philipparndt/opentherm-wolf-cwl/openspec/changes/archive/2026-04-25-esp32-documentation/tasks.md

## 1. Documentation

- [x] 1.1 Create `esp32/README.md` — hardware components, wiring, build/flash instructions, configuration, MQTT reference, OLED/encoder usage
