philipparndt/opentherm-wolf-cwl/openspec/changes/archive/2026-04-26-schedule-list-grouping/tasks.md

## 1. Implementation

- [x] 1.1 Update `daysStr()` in web UI `App.tsx` — return "Every day", "Weekdays", "Weekend", or individual days
- [x] 1.2 Update `getActiveScheduleDescription()` in `scheduler.cpp` — same grouping logic for OLED/MQTT
- [x] 1.3 Build verification — SUCCESS
