philipparndt/opentherm-wolf-cwl/openspec/changes/archive/2026-04-26-schedule-timeline-view/tasks.md

## 1. Implementation

- [x] 1.1 Create `WeekTimeline` component in `App.tsx` — compute per-day coverage from schedule entries, render colored segments + gap segments with first-match logic, midnight-spanning support
- [x] 1.2 Add timeline CSS in `style.css` — day rows, colored segments, striped gap pattern, time axis ticks, legend, responsive
- [x] 1.3 Add `WeekTimeline` to the Schedules tab above the grouped list
- [x] 1.4 Build verification — SUCCESS (29.6KB JS)
