philipparndt/opentherm-wolf-cwl/esp32/src/i18n.rs

//! Internationalization — English and German string tables for the OLED display.

#[derive(Debug, Clone, Copy, PartialEq)]
pub enum Language {
    En = 0,
    De = 1,
}

impl Language {
    pub fn from_u8(v: u8) -> Self {
        match v {
            1 => Self::De,
            _ => Self::En,
        }
    }

    pub fn code(self) -> &'static str {
        match self {
            Self::En => "en",
            Self::De => "de",
        }
    }

    pub fn from_code(s: &str) -> Self {
        match s {
            "de" => Self::De,
            _ => Self::En,
        }
    }
}

pub struct Strings {
    // Page headers
    pub ventilation: &'static str,
    pub scheduled: &'static str,
    pub manual: &'static str,
    pub set_level: &'static str,
    pub off_duration: &'static str,
    pub summer_mode: &'static str,
    pub set_mode: &'static str,
    pub intake: &'static str,
    pub status: &'static str,
    pub system: &'static str,
    pub settings: &'static str,

    // Ventilation levels
    pub level_off: &'static str,
    pub level_reduced: &'static str,
    pub level_normal: &'static str,
    pub level_party: &'static str,
    pub level_schedule: &'static str,

    // Bypass / mode
    pub summer: &'static str,
    pub winter: &'static str,
    pub active: &'static str,
    pub inactive: &'static str,
    pub bypass_open_desc: &'static str,
    pub heat_recovery_desc: &'static str,

    // Status labels
    pub filter: &'static str,
    pub mode: &'static str,
    pub airflow: &'static str,
    pub replace: &'static str,
    pub ok: &'static str,

    // System labels
    pub net_connected: &'static str,
    pub net_disconnected: &'static str,
    pub mqtt_online: &'static str,
    pub mqtt_offline: &'static str,
    pub uptime_prefix: &'static str,
    pub boot_prefix: &'static str,

    // Edit hints
    pub hint_rotate_adjust: &'static str,
    pub hint_rotate_hours: &'static str,
    pub hint_rotate_toggle: &'static str,

    // Overlays
    pub connected: &'static str,
    pub disconnected: &'static str,
    pub no_network: &'static str,
    pub cwl_disconnected: &'static str,

    // Boot
    pub connecting: &'static str,

    // Temp labels
    pub supply: &'static str,
    pub exhaust: &'static str,

    // Settings page
    pub language_label: &'static str,
    pub english: &'static str,
    pub deutsch: &'static str,

    // Timed off
    pub resumes_in: &'static str,

    // Temperature history pages
    pub outdoor_24h: &'static str,
    pub indoor_24h: &'static str,
    pub min_label: &'static str,
    pub max_label: &'static str,
    pub history_empty: &'static str,
    pub celsius_unit: &'static str,
}

pub const EN: Strings = Strings {
    ventilation: "Ventilation",
    scheduled: "Scheduled",
    manual: "Manual",
    set_level: "Set Level",
    off_duration: "Off Duration",
    summer_mode: "Summer Mode",
    set_mode: "Set Mode",
    intake: "Intake",
    status: "Status",
    system: "System",
    settings: "Settings",

    level_off: "Off",
    level_reduced: "Reduced",
    level_normal: "Normal",
    level_party: "Party",
    level_schedule: "Schedule",

    summer: "Summer",
    winter: "Winter",
    active: "Active",
    inactive: "Inactive",
    bypass_open_desc: "Bypass open - free cooling",
    heat_recovery_desc: "Heat recovery active",

    filter: "Filter:",
    mode: "Mode:",
    airflow: "Airflow:",
    replace: "REPLACE",
    ok: "OK",

    net_connected: "Net: connected",
    net_disconnected: "Net: disconnected",
    mqtt_online: "MQTT: online",
    mqtt_offline: "MQTT: offline",
    uptime_prefix: "Up:",
    boot_prefix: "Boot:",

    hint_rotate_adjust: "rotate: adjust  press: ok",
    hint_rotate_hours: "rotate: hours  press: ok",
    hint_rotate_toggle: "rotate: toggle  press: ok",

    connected: "Connected",
    disconnected: "Disconnected",
    no_network: "No network",
    cwl_disconnected: "Disconnected",

    connecting: "Connecting...",

    supply: "Supply:",
    exhaust: "Exhaust:",

    language_label: "Language",
    english: "English",
    deutsch: "Deutsch",

    resumes_in: "Resumes in",

    outdoor_24h: "Outdoor 24h",
    indoor_24h: "Indoor 24h",
    min_label: "Min",
    max_label: "Max",
    history_empty: "Collecting...",
    celsius_unit: "C",
};

pub const DE: Strings = Strings {
    ventilation: "L\u{fc}ftung",
    scheduled: "Zeitplan",
    manual: "Manuell",
    set_level: "Stufe",
    off_duration: "Aus-Dauer",
    summer_mode: "Sommermodus",
    set_mode: "Modus",
    intake: "Zuluft",
    status: "Status",
    system: "System",
    settings: "Einstellungen",

    level_off: "Aus",
    level_reduced: "Reduziert",
    level_normal: "Normal",
    level_party: "Party",
    level_schedule: "Zeitplan",

    summer: "Sommer",
    winter: "Winter",
    active: "Aktiv",
    inactive: "Inaktiv",
    bypass_open_desc: "Bypass offen - K\u{fc}hlung",
    heat_recovery_desc: "W\u{e4}rmer\u{fc}ckgewinnung",

    filter: "Filter:",
    mode: "Modus:",
    airflow: "Luftstrom:",
    replace: "WECHSELN",
    ok: "OK",

    net_connected: "Netz: verbunden",
    net_disconnected: "Netz: getrennt",
    mqtt_online: "MQTT: online",
    mqtt_offline: "MQTT: offline",
    uptime_prefix: "An:",
    boot_prefix: "Start:",

    hint_rotate_adjust: "drehen: w\u{e4}hlen  dr\u{fc}cken: ok",
    hint_rotate_hours: "drehen: Stunden  dr\u{fc}cken: ok",
    hint_rotate_toggle: "drehen: umschalten  dr\u{fc}cken: ok",

    connected: "Verbunden",
    disconnected: "Getrennt",
    no_network: "Kein Netzwerk",
    cwl_disconnected: "Getrennt",

    connecting: "Verbinde...",

    supply: "Zuluft:",
    exhaust: "Abluft:",

    language_label: "Sprache",
    english: "English",
    deutsch: "Deutsch",

    resumes_in: "Weiter in",

    outdoor_24h: "Au\u{df}en 24h",
    indoor_24h: "Innen 24h",
    min_label: "Min",
    max_label: "Max",
    history_empty: "Sammle...",
    celsius_unit: "C",
};

pub fn tr(lang: Language) -> &'static Strings {
    match lang {
        Language::En => &EN,
        Language::De => &DE,
    }
}

/// Get level name in the active language
pub fn level_name(lang: Language, level: u8) -> &'static str {
    let s = tr(lang);
    match level {
        0 => s.level_off,
        1 => s.level_reduced,
        2 => s.level_normal,
        3 => s.level_party,
        4 => s.level_schedule,
        _ => s.level_normal,
    }
}
